esprit1711/Switch-Ornament/how-to/Anleitung/Switch_render_2.png

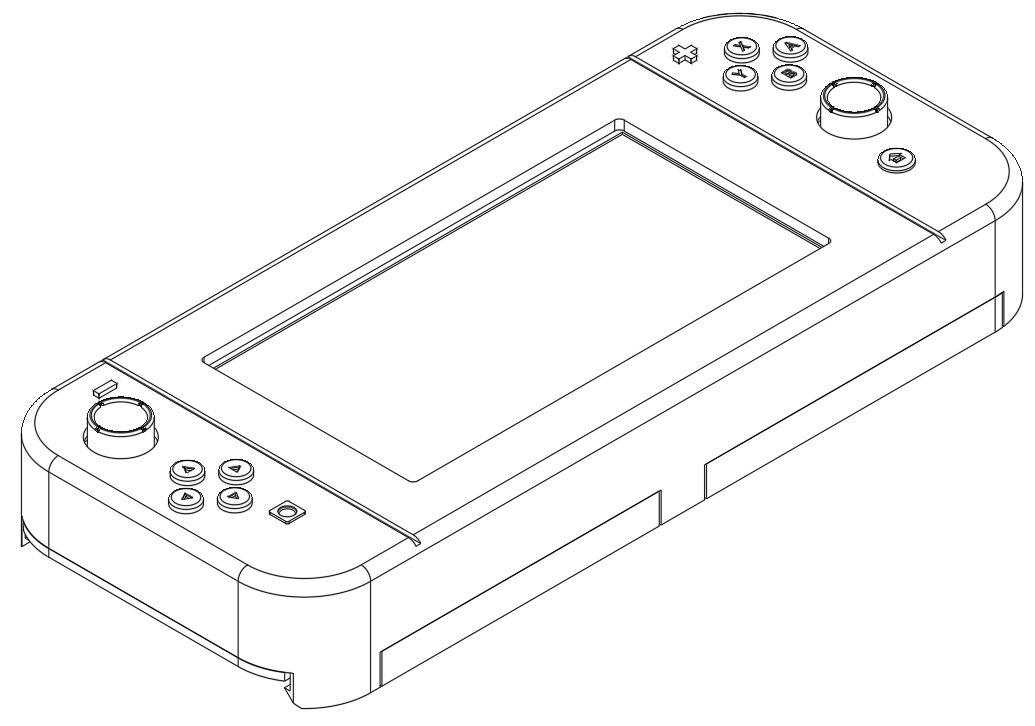
how-to/Anleitung/Switch_render_2.png
