esprit1711/Switch-Ornament/how-to/Pictures/IMG_20230401_140933.jpg

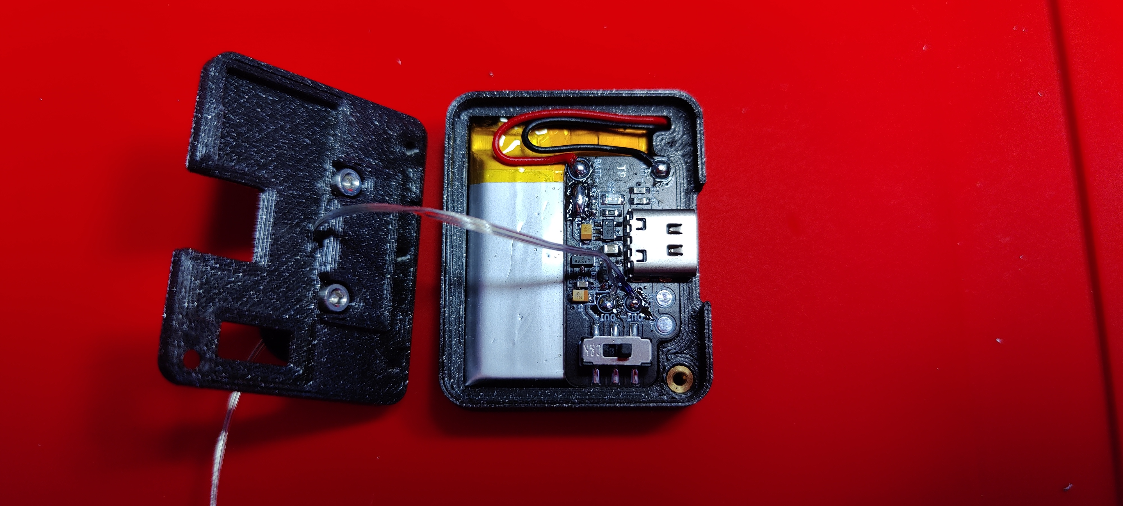
how-to/Pictures/IMG_20230401_140933.jpg
