esprit1711/Switch-Ornament/how-to/Pictures/IMG_20230401_150318.jpg

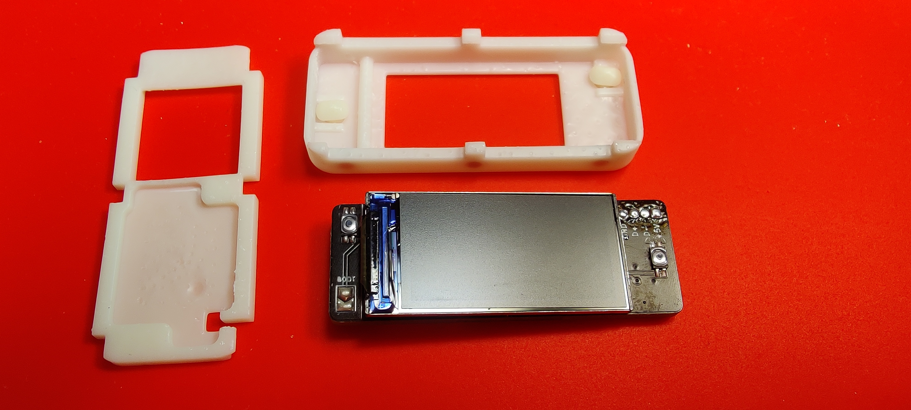
how-to/Pictures/IMG_20230401_150318.jpg
