esprit1711/Switch-Ornament/how-to/Pictures/IMG_20230401_194840.jpg

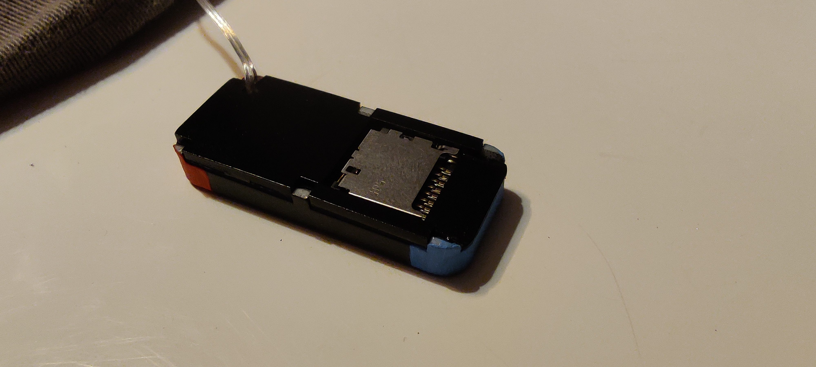
how-to/Pictures/IMG_20230401_194840.jpg
